JoseOlin/Akoui-Grua/assets/imgs/01_Muestra de operación de la grúa con valeroso modelo.jpg

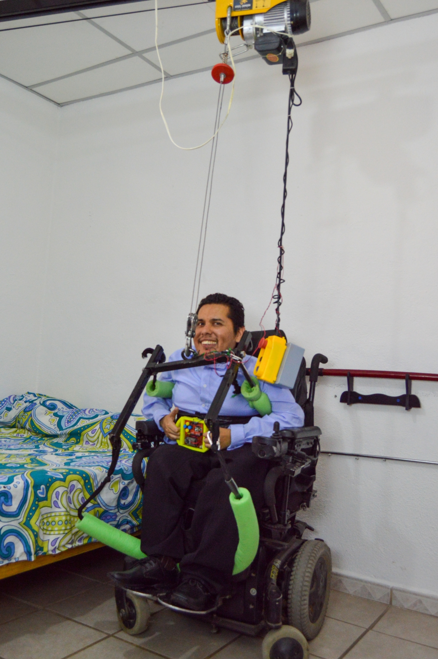
assets/imgs/01_Muestra de operación de la grúa con valeroso modelo.jpg
