JoseOlin/Akoui-Grua/assets/imgs/01_Módulos_Akoui.jpeg

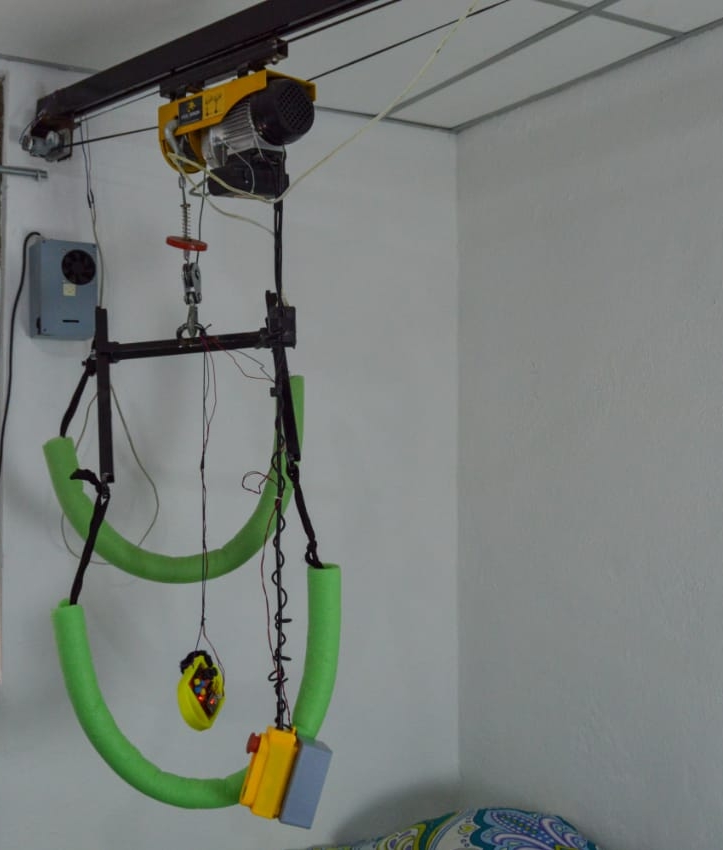
assets/imgs/01_Módulos_Akoui.jpeg
