JoseOlin/Akoui-Grua/assets/imgs/01_Módulos_Akoui_labeled.png

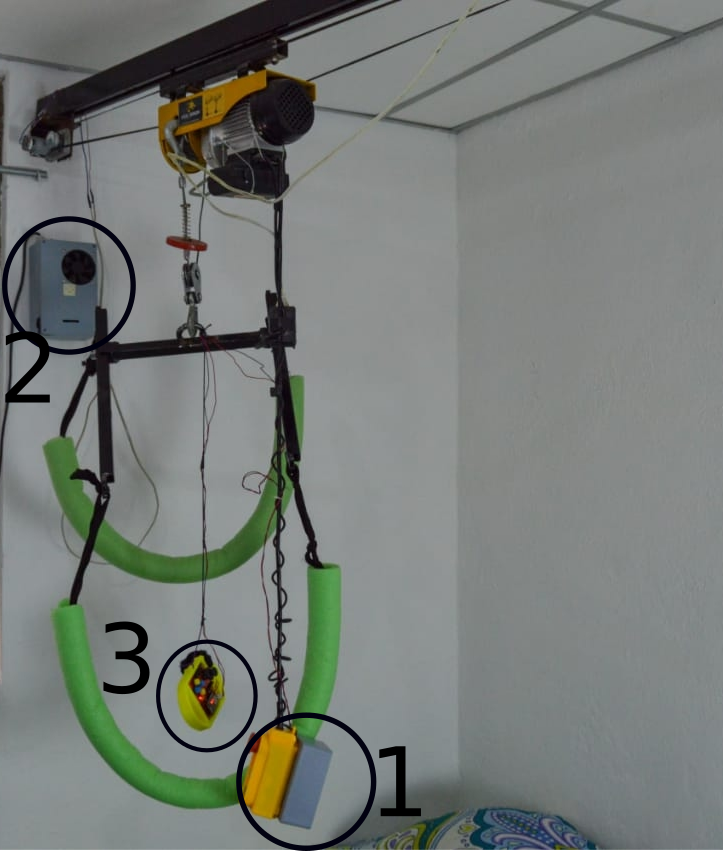
assets/imgs/01_Módulos_Akoui_labeled.png
