JoseOlin/Akoui-Grua/assets/imgs/04_Control de la grúa.png

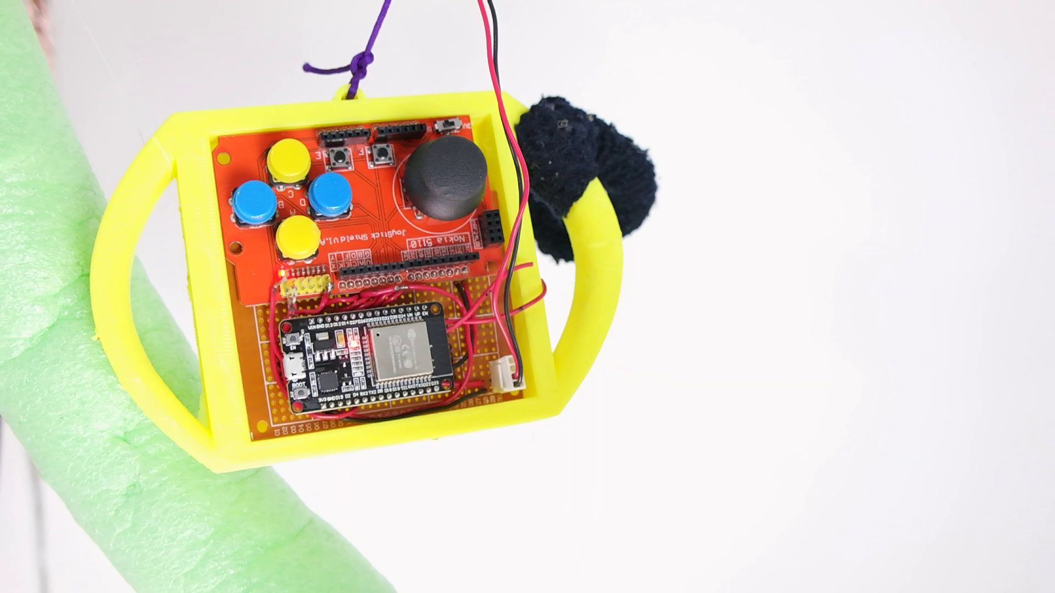
assets/imgs/04_Control de la grúa.png
