JoseOlin/Akoui-Grua/assets/imgs/05_a. Grúa y rieles utilizados para la Akoui.jpeg

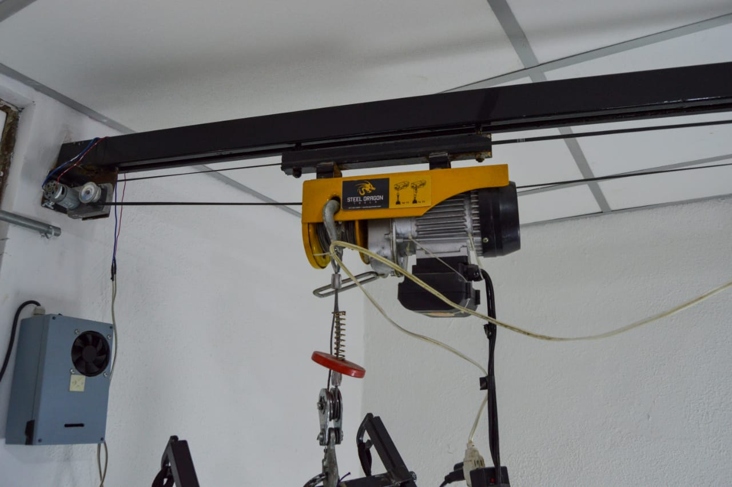
assets/imgs/05_a. Grúa y rieles utilizados para la Akoui.jpeg
