JoseOlin/Akoui-Grua/assets/imgs/diagrama-akoui-pad-control (copia).jpeg

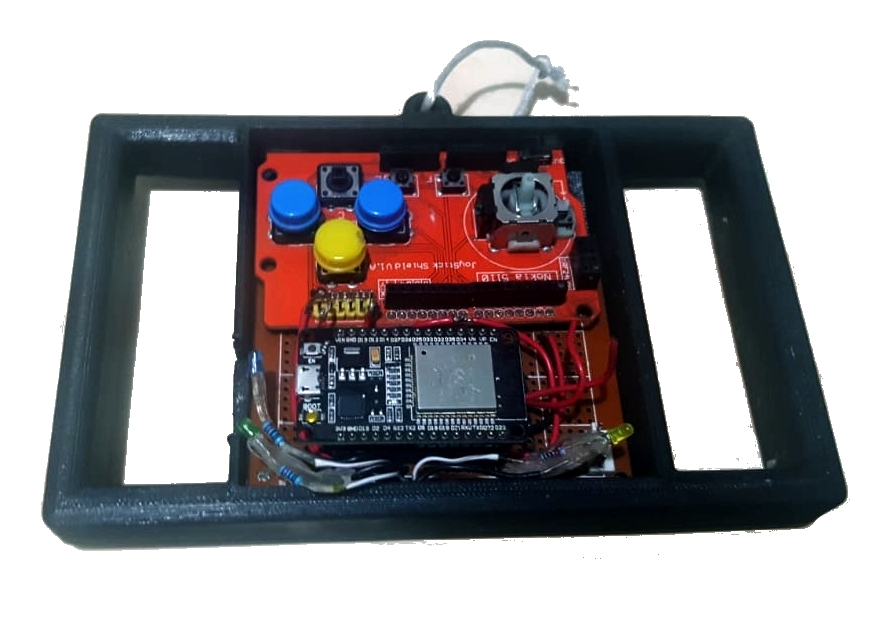
assets/imgs/diagrama-akoui-pad-control (copia).jpeg
