JoseOlin/Akoui-Grua/assets/imgs/IMG_20220910_122807.jpg

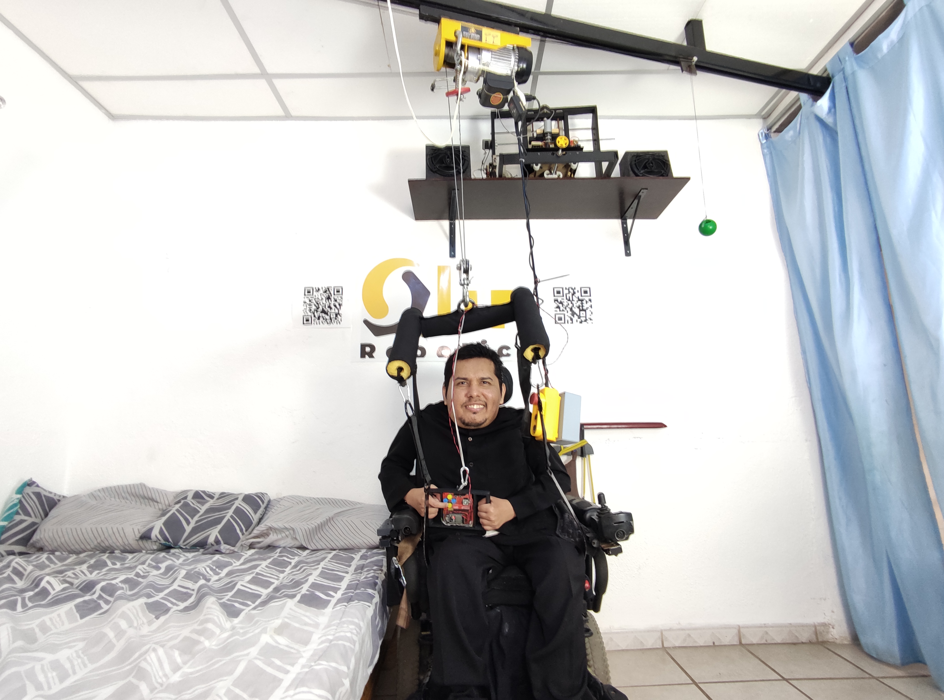
assets/imgs/IMG_20220910_122807.jpg
