JoseOlin/Akoui-Grua/Hardware/Control_Pad/Electronics/Akoui-Pad-Control-Circuit_bb.png

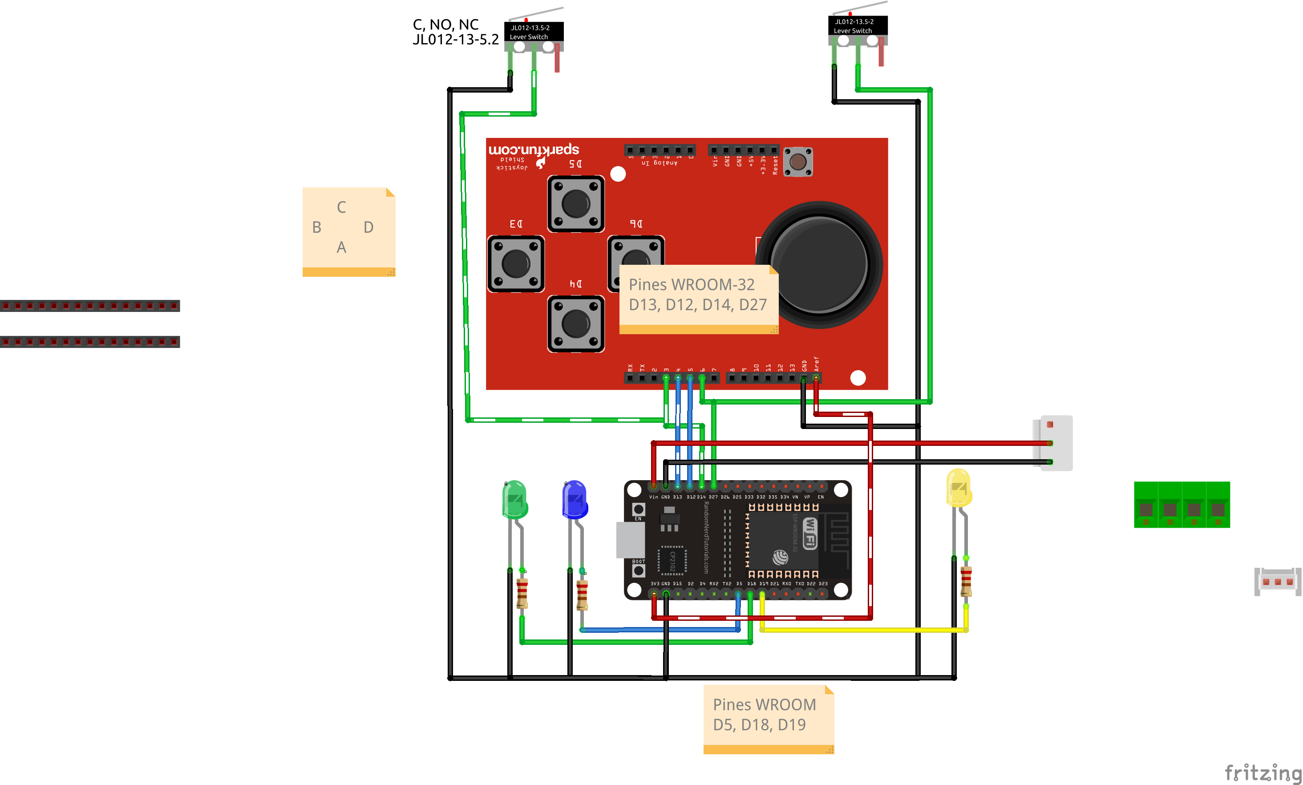
Hardware/Control_Pad/Electronics/Akoui-Pad-Control-Circuit_bb.png
