JoseOlin/Akoui-Grua/Hardware/ModuloControl_Horizontal/Electrónica/PololuMC33926/Pololu_MC33926_pinout.jpg

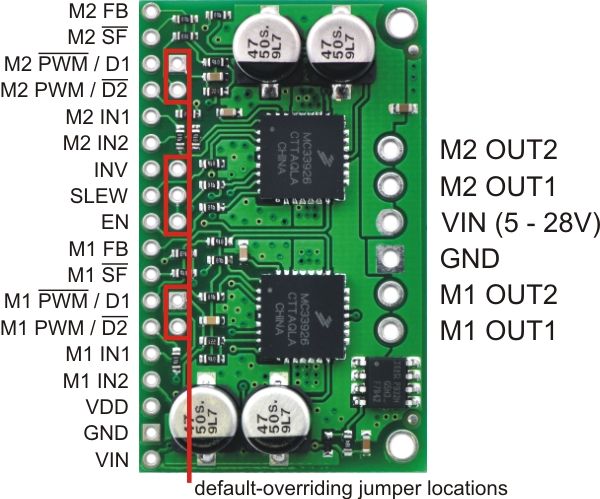
Hardware/ModuloControl_Horizontal/Electrónica/PololuMC33926/Pololu_MC33926_pinout.jpg
