JoseOlin/Akoui-Grua/Hardware/ModuloControl_Horizontal/Electrónica/WeMos_D1_Mini_V2/2dc7d4435c7c950a1209d946ffa383f3e9c8b8a3_2_690x428.jpeg

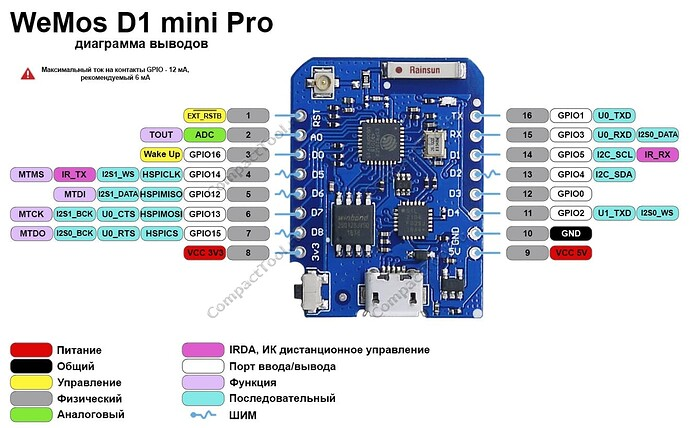
Hardware/ModuloControl_Horizontal/Electrónica/WeMos_D1_Mini_V2/2dc7d4435c7c950a1209d946ffa383f3e9c8b8a3_2_690x428.jpeg
