JoseOlin/Akoui-Grua/Hardware/ModuloControl_Vertical/Electrónica/Circuito/3adffb0e-eeb6-4fb7-9969-0489ad38aaa7.jpeg

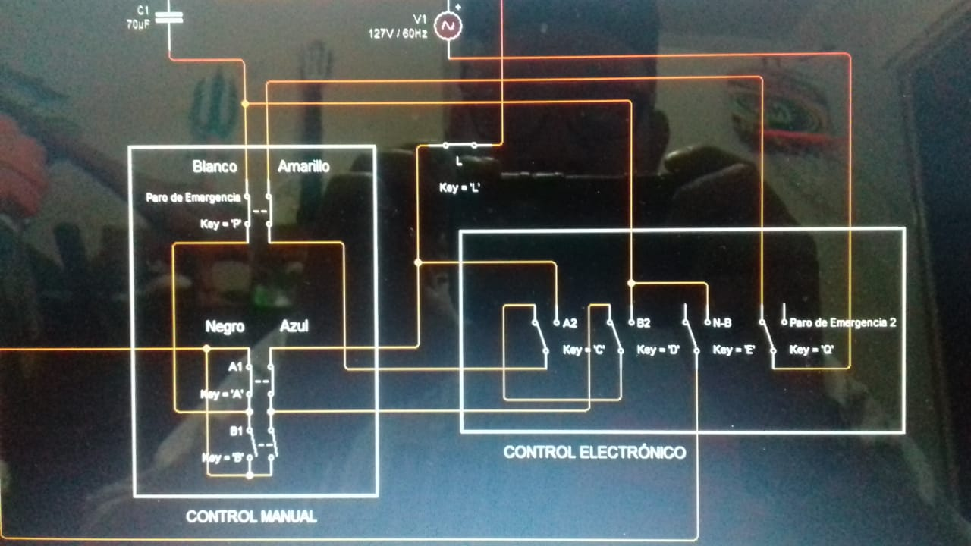
Hardware/ModuloControl_Vertical/Electrónica/Circuito/3adffb0e-eeb6-4fb7-9969-0489ad38aaa7.jpeg
