JoseOlin/Akoui-Grua/Hardware/Riel y Polipasto/36561751_1978189882211582_5358359271018856448_n.jpg

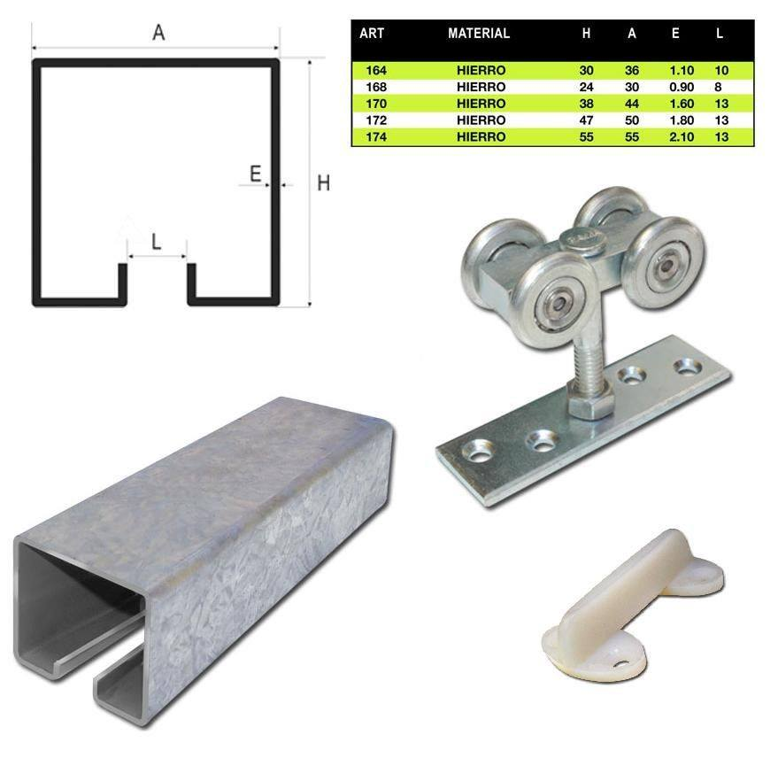
Hardware/Riel y Polipasto/36561751_1978189882211582_5358359271018856448_n.jpg
