JoseOlin/Akoui-Grua/Software/Control_Desktop_QtCreator/ControlGrua_Qt_TCP/imgs/down.jpeg

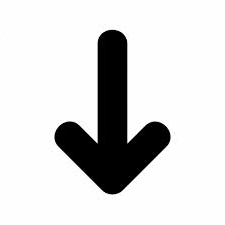
Software/Control_Desktop_QtCreator/ControlGrua_Qt_TCP/imgs/down.jpeg
