JoseOlin/Akoui-Grua/Software/Control_Desktop_QtCreator/ControlGrua_Qt_TCP/imgs/emergency_pressed.jpg

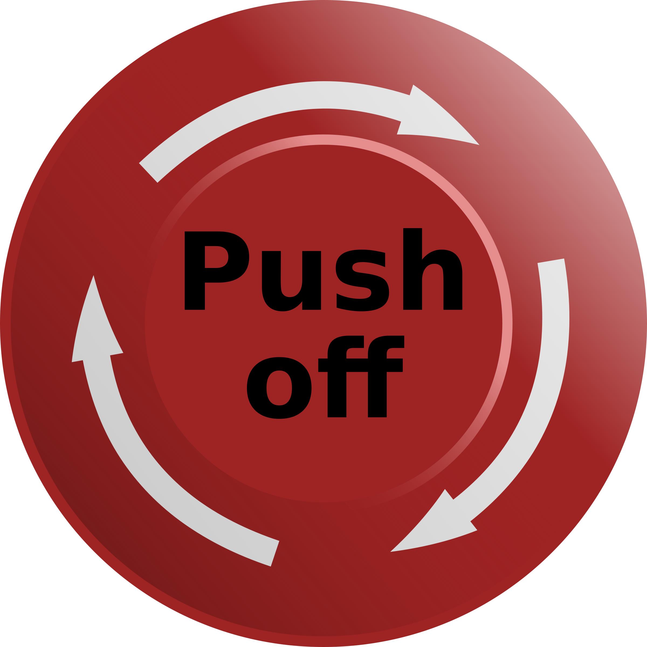
Software/Control_Desktop_QtCreator/ControlGrua_Qt_TCP/imgs/emergency_pressed.jpg
