JoseOlin/Akoui-Grua/Software/Control_Desktop_QtCreator/ControlGrua_Qt_TCP/imgs/emergency_released.png

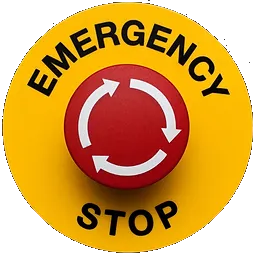
Software/Control_Desktop_QtCreator/ControlGrua_Qt_TCP/imgs/emergency_released.png
