JoseOlin/Akoui-Grua/Hardware/ModuloControl_Vertical/Electrónica/Circuito/Diagrama_ControlManual_Relevadores.jpeg

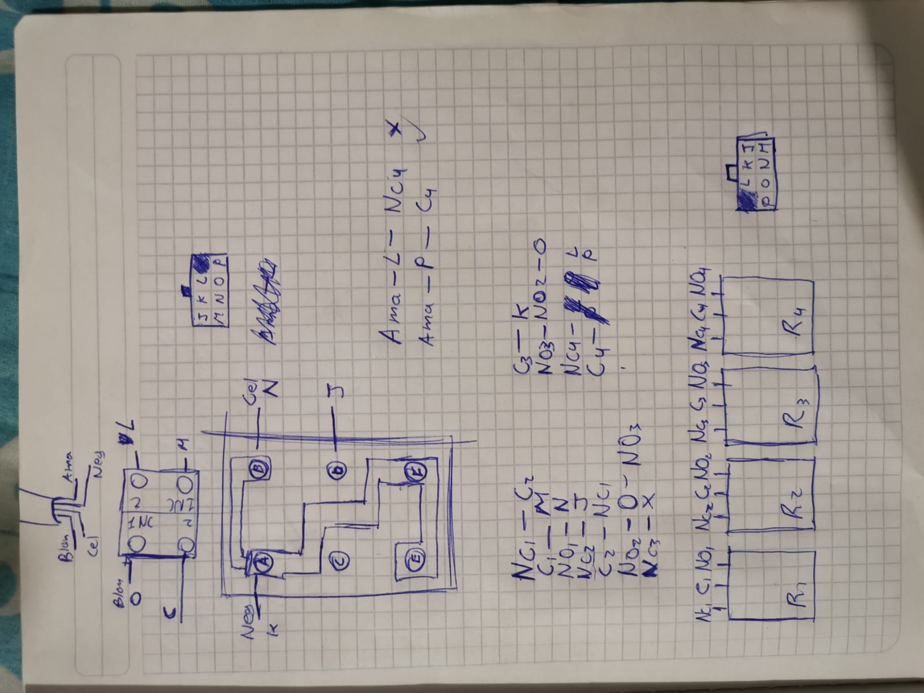
Hardware/ModuloControl_Vertical/Electrónica/Circuito/Diagrama_ControlManual_Relevadores.jpeg
