JoseOlin/Akoui-Grua/Hardware/ModuloControl_Vertical/Electrónica/Circuito/MandoManual2.jpeg

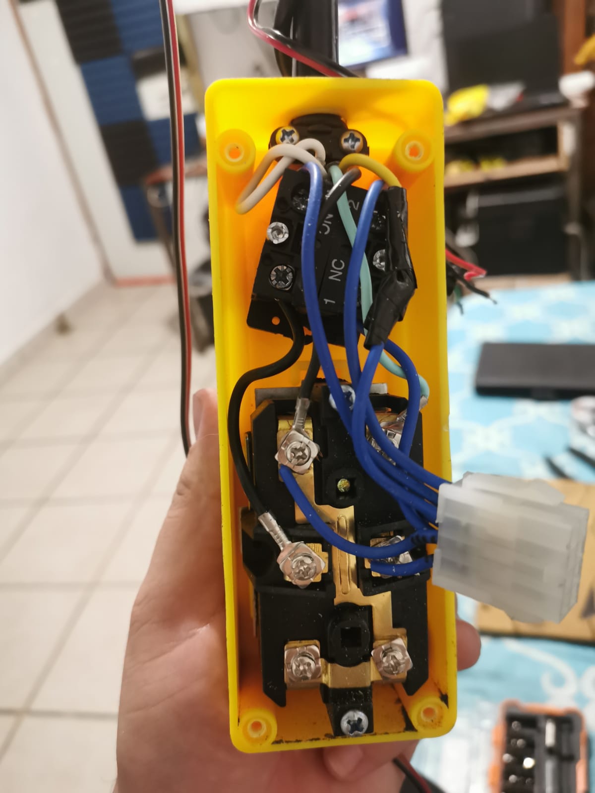
Hardware/ModuloControl_Vertical/Electrónica/Circuito/MandoManual2.jpeg
