JoseOlin/Akoui-Grua/Hardware/ModuloControl_Vertical/Electrónica/Circuito/MandoManual.jpeg

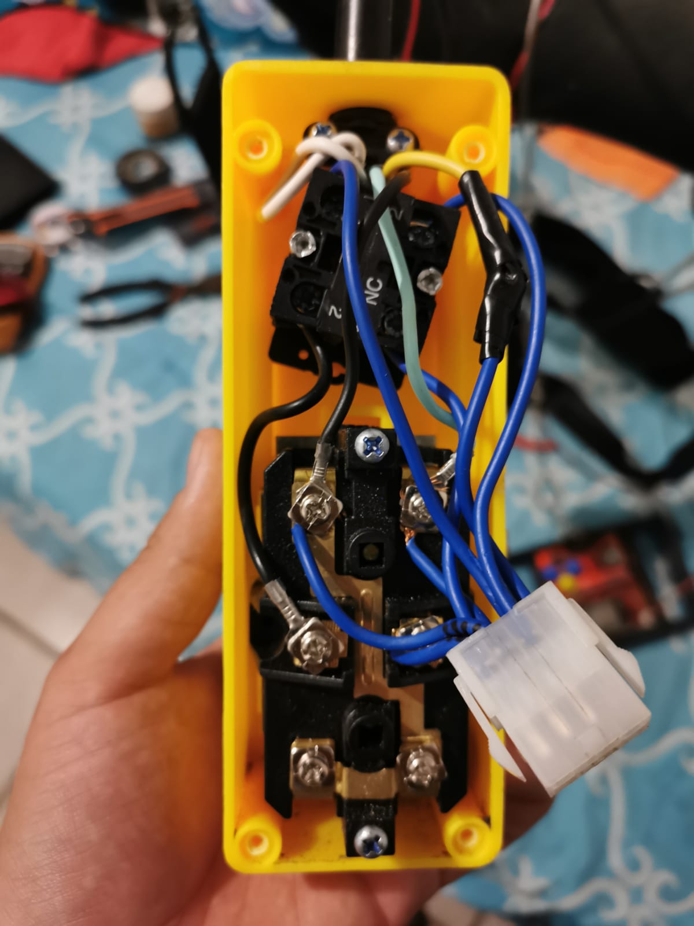
Hardware/ModuloControl_Vertical/Electrónica/Circuito/MandoManual.jpeg
