JoseOlin/Akoui-Grua/Manuals/Manual_Construcción/ControlPad_Construccion/akoui-pio-monitor-con-conexion.gif

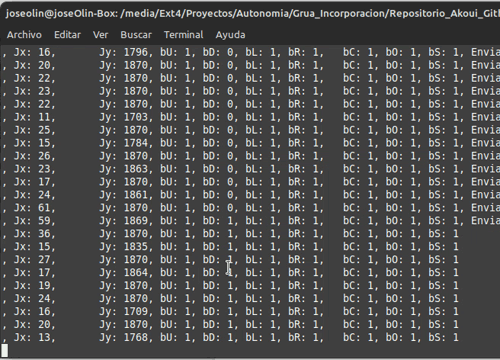
Manuals/Manual_Construcción/ControlPad_Construccion/akoui-pio-monitor-con-conexion.gif
