JoseOlin/Akoui-Grua/Manuals/Manual_Construcción/Instalacion_Riel/imgs/GruaInstalada-2.jpeg

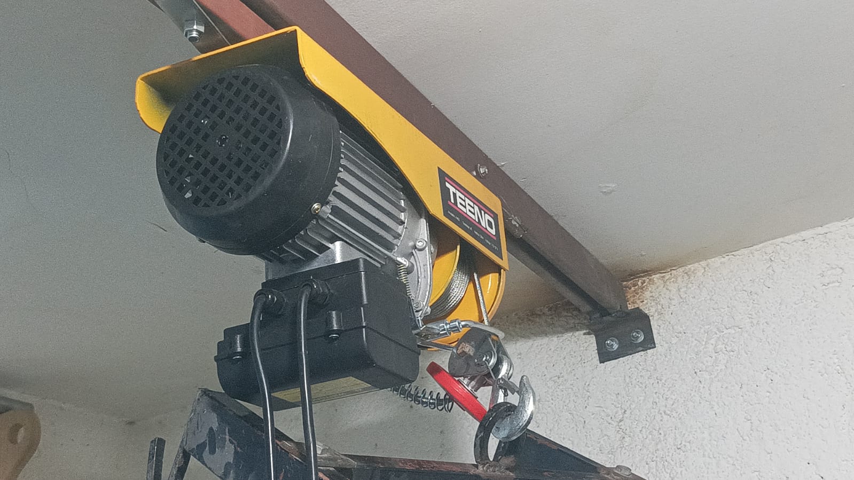
Manuals/Manual_Construcción/Instalacion_Riel/imgs/GruaInstalada-2.jpeg
