JoseOlin/Akoui-Grua/Manuals/Manual_Construcción/Instalacion_Riel/imgs/Instalacion-riel-2.JPG

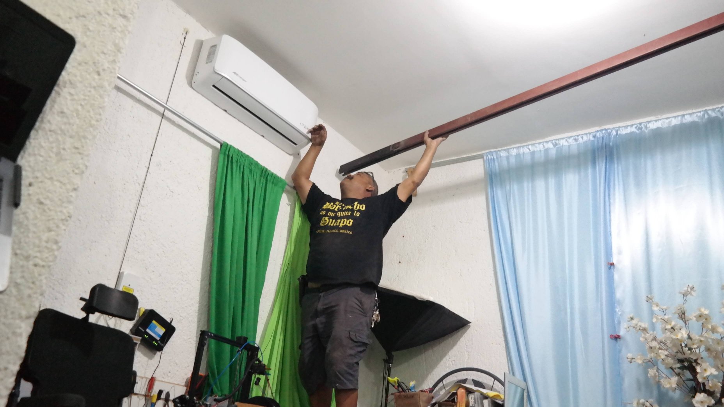
Manuals/Manual_Construcción/Instalacion_Riel/imgs/Instalacion-riel-2.JPG
