JoseOlin/Akoui-Grua/Manuals/Manual_Construcción/Instalacion_Riel/imgs/Instalacion-riel-5.JPG

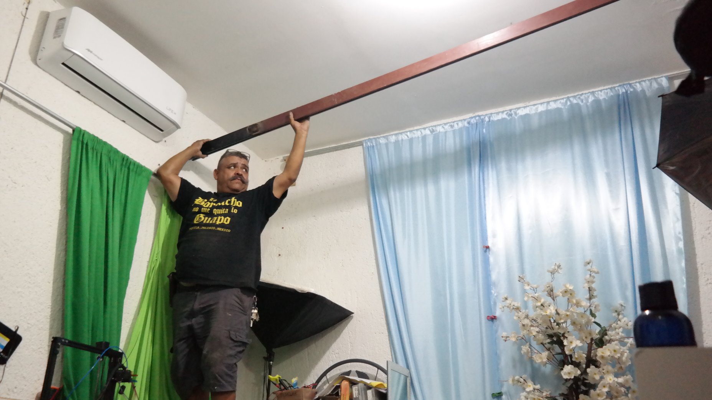
Manuals/Manual_Construcción/Instalacion_Riel/imgs/Instalacion-riel-5.JPG
