JoseOlin/Akoui-Grua/Manuals/Manual_Construcción/Instalacion_Riel/imgs/Instalacion-riel-6.jpeg

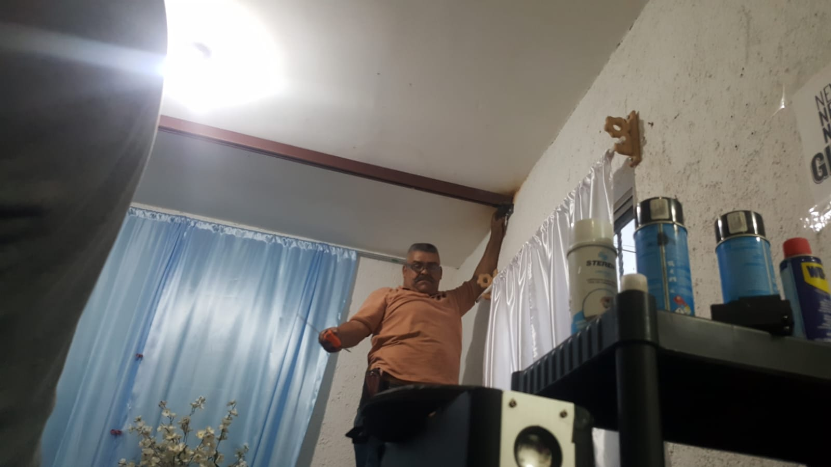
Manuals/Manual_Construcción/Instalacion_Riel/imgs/Instalacion-riel-6.jpeg
