JoseOlin/Akoui-Grua/Manuals/Manual_Construcción/Instalacion_Riel/imgs/Instalacion-riel-7.jpeg

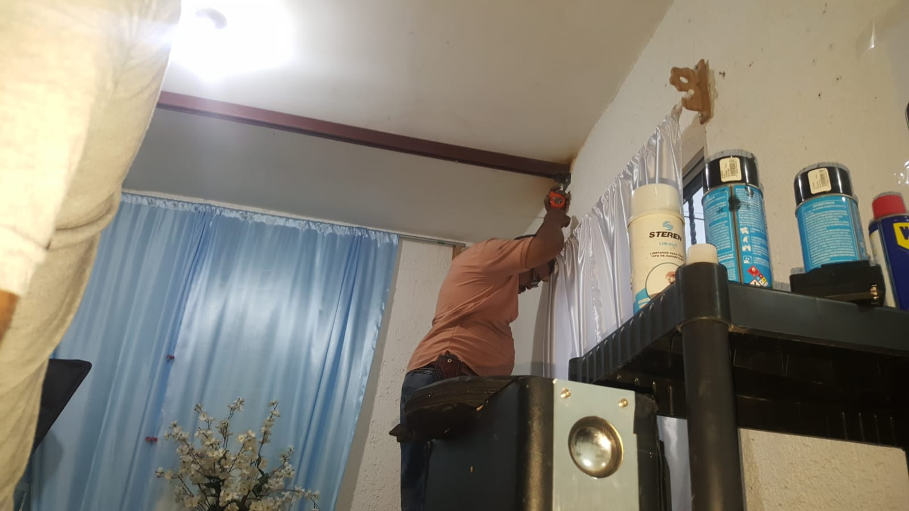
Manuals/Manual_Construcción/Instalacion_Riel/imgs/Instalacion-riel-7.jpeg
