JoseOlin/Akoui-Grua/Manuals/Manual_Construcción/Instalacion_Riel/imgs/Soporte-Angular-Instalado_4.jpeg

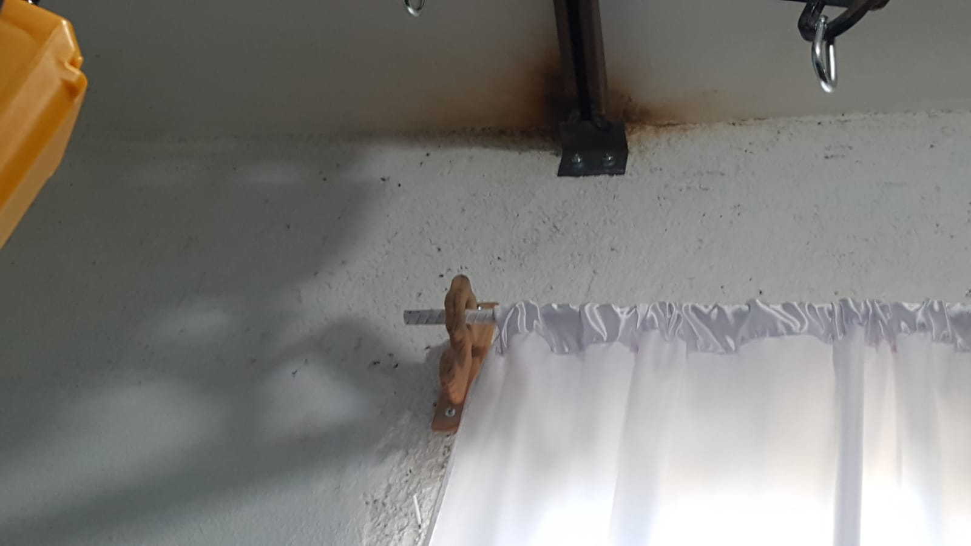
Manuals/Manual_Construcción/Instalacion_Riel/imgs/Soporte-Angular-Instalado_4.jpeg
