JoseOlin/Akoui-Grua/Manuals/Manual_Construcción/Instalacion_Riel/imgs/Soporte-Angular-Instalado_5.jpeg

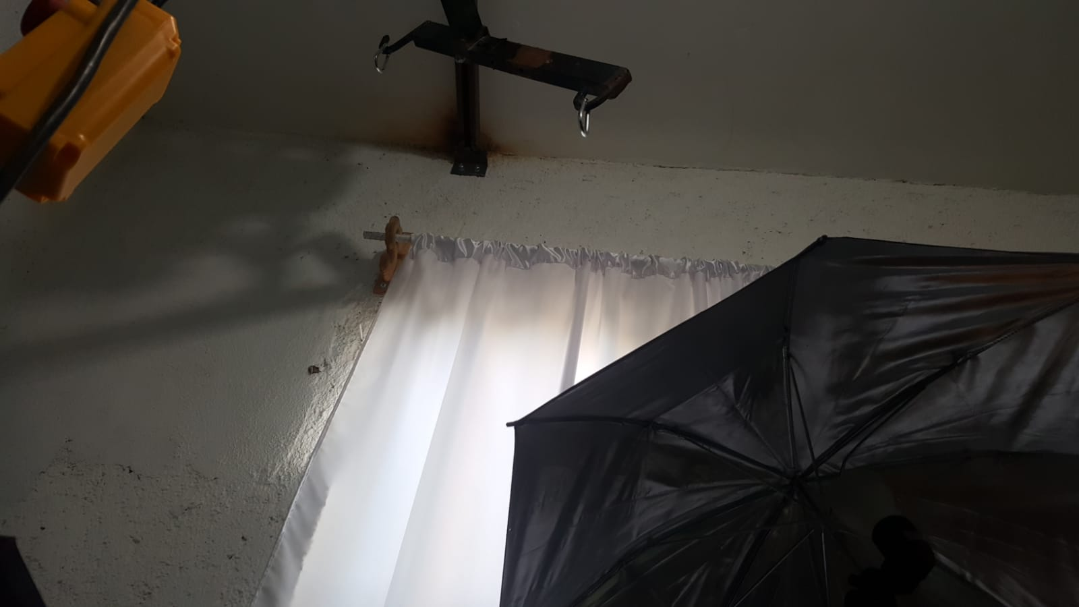
Manuals/Manual_Construcción/Instalacion_Riel/imgs/Soporte-Angular-Instalado_5.jpeg
