JoseOlin/Akoui-Grua/Manuals/Manual_Construcción/Instalacion_Riel/imgs/Soportes_Angulares_8.jpeg

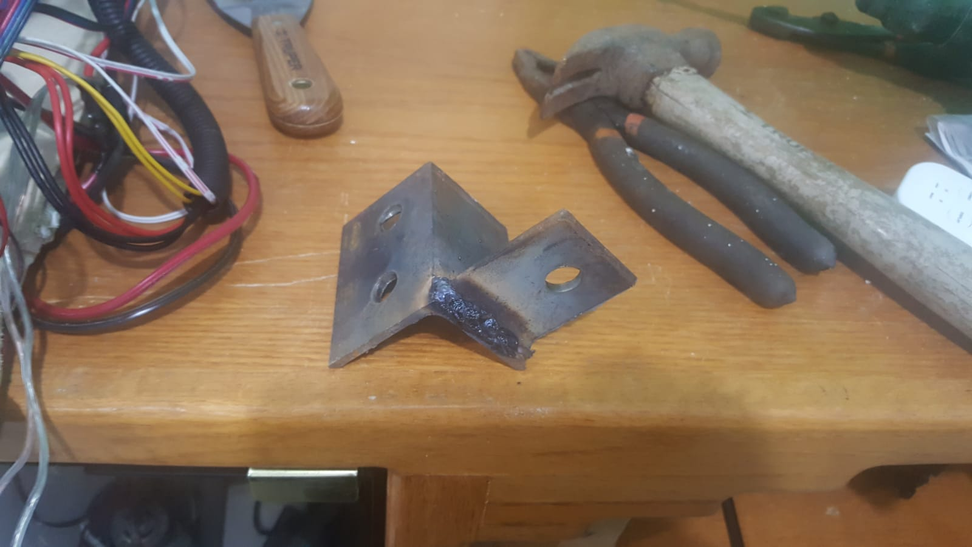
Manuals/Manual_Construcción/Instalacion_Riel/imgs/Soportes_Angulares_8.jpeg
