JoseOlin/Akoui-Grua/Manuals/Manual_Construcción/Instalacion_Riel/imgs/Soportes_Angulares_9.jpeg

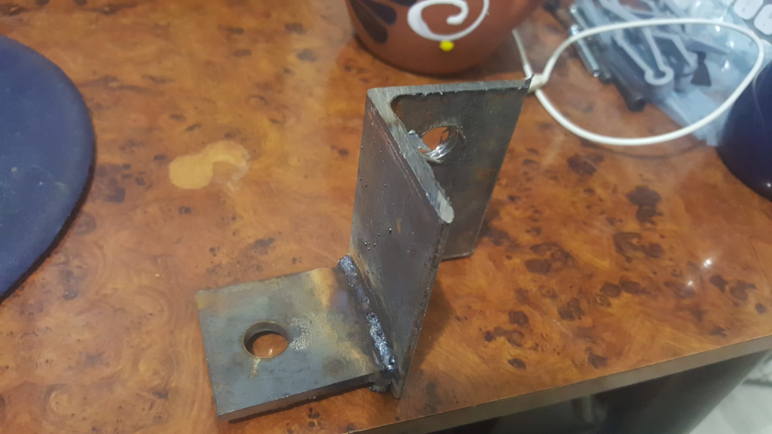
Manuals/Manual_Construcción/Instalacion_Riel/imgs/Soportes_Angulares_9.jpeg
