JoseOlin/Akoui-Grua/Manuals/Manual_Construcción/Instalacion_Riel/imgs/taquetes_6.jpeg

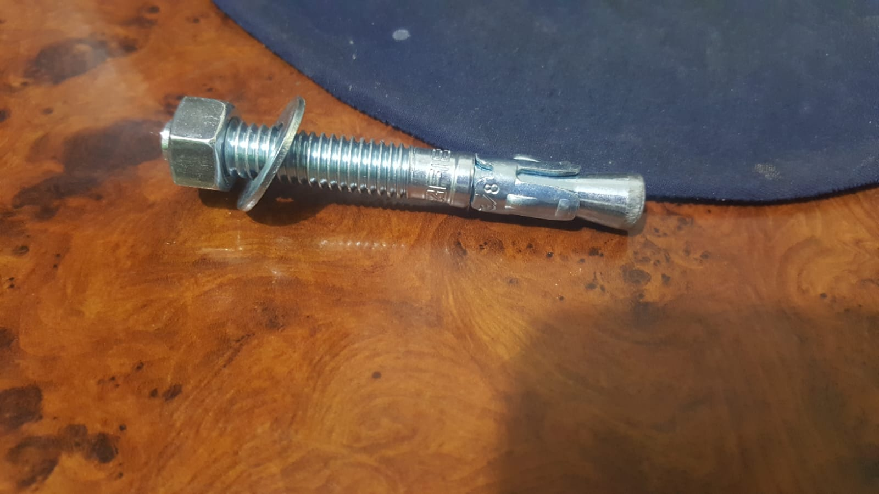
Manuals/Manual_Construcción/Instalacion_Riel/imgs/taquetes_6.jpeg
