JoseOlin/Akoui-Grua/Manuals/Manual_Construcción/Instalacion_Riel/imgs/Tornillo_3-8_3.jpeg

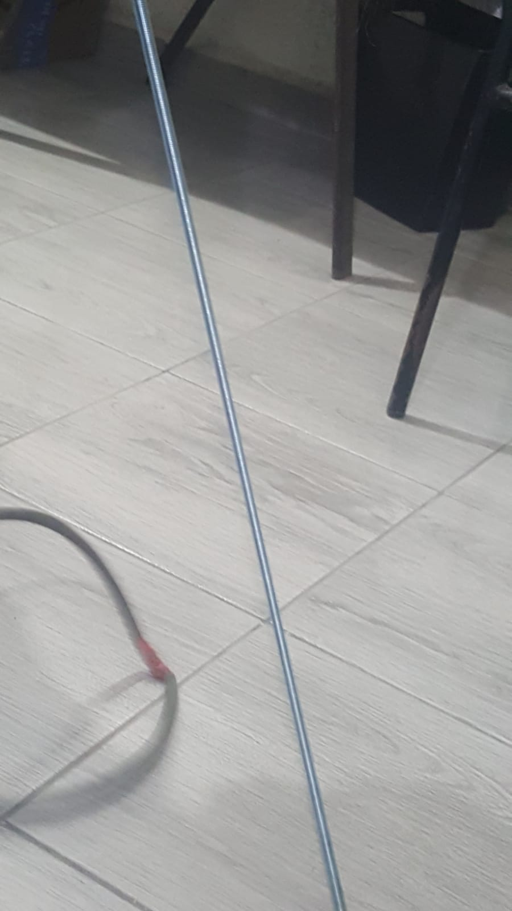
Manuals/Manual_Construcción/Instalacion_Riel/imgs/Tornillo_3-8_3.jpeg
