JoseOlin/Akoui-Grua/Manuals/Manual_Construcción/Instalacion_Riel/imgs/Tornillo_3-8_Recortado_1.JPG

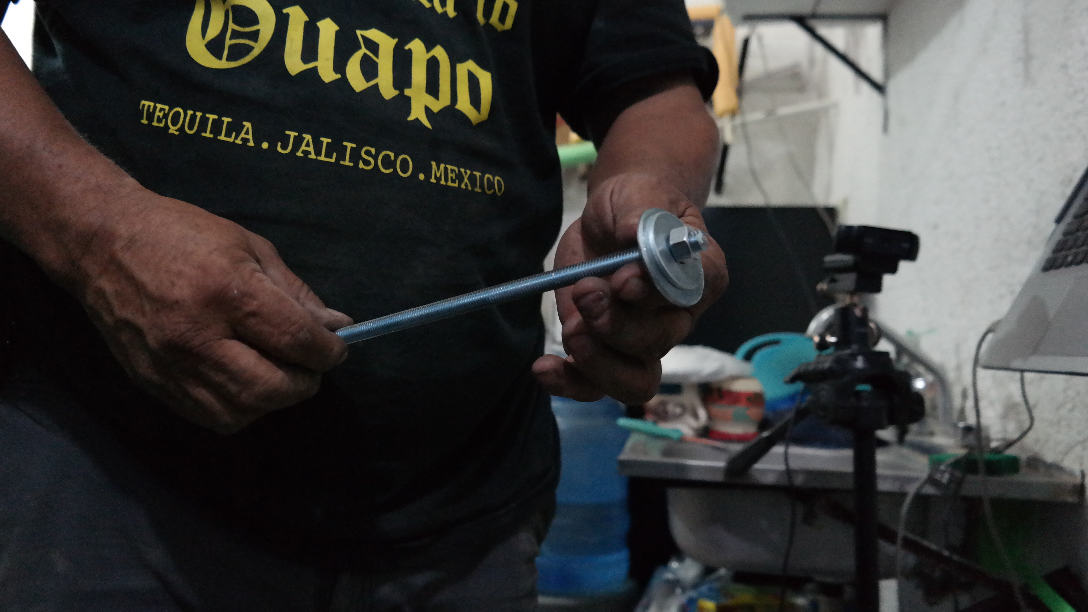
Manuals/Manual_Construcción/Instalacion_Riel/imgs/Tornillo_3-8_Recortado_1.JPG
