JoseOlin/Akoui-Grua/Manuals/Manual_Mantenimiento/imgs/7e57e645-24a5-4c56-a8ba-4ad31c3c1ef6.jpeg

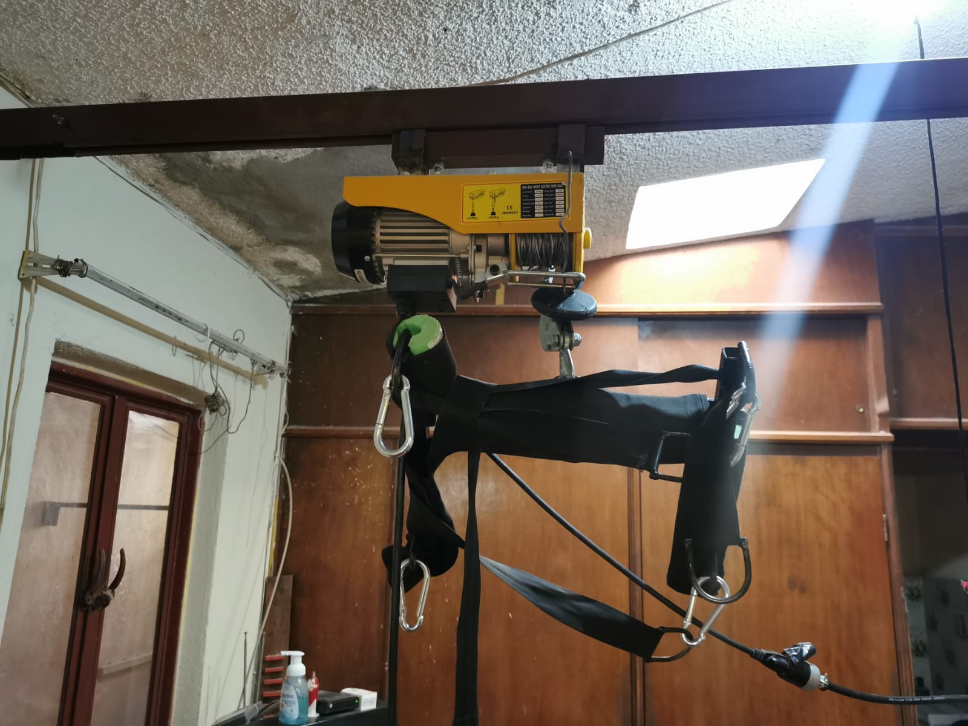
Manuals/Manual_Mantenimiento/imgs/7e57e645-24a5-4c56-a8ba-4ad31c3c1ef6.jpeg
