JoseOlin/Akoui-Grua/Manuals/Manual_Mantenimiento/imgs/87ca44ee-71d5-4784-a0d1-1c792c2dc31c.jpeg

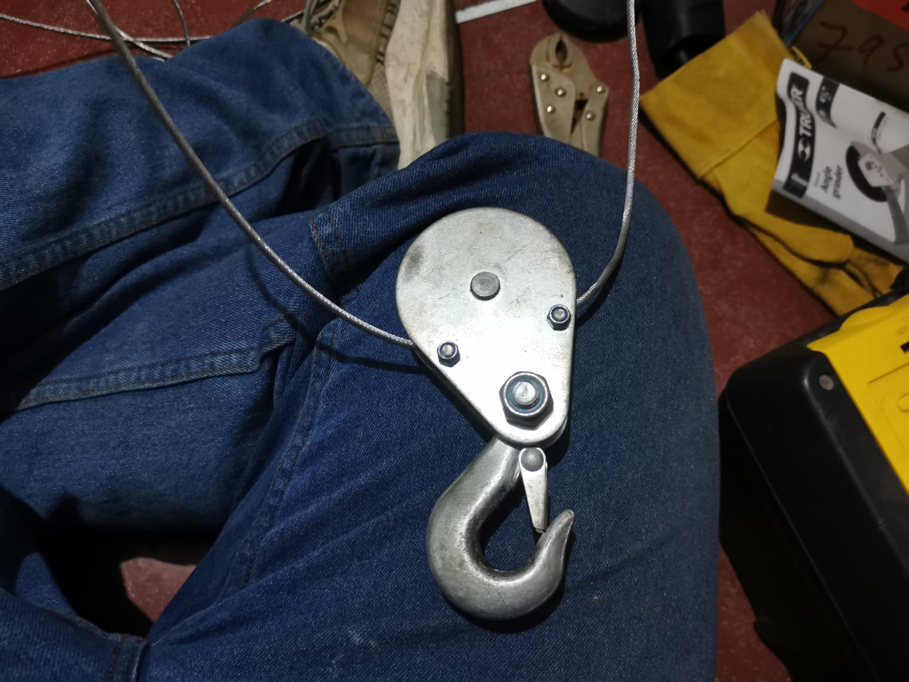
Manuals/Manual_Mantenimiento/imgs/87ca44ee-71d5-4784-a0d1-1c792c2dc31c.jpeg
