JoseOlin/Akoui-Grua/Manuals/Manual_Mantenimiento/imgs/94c086cd-e113-414c-a847-a976a1d2ec9f.jpeg

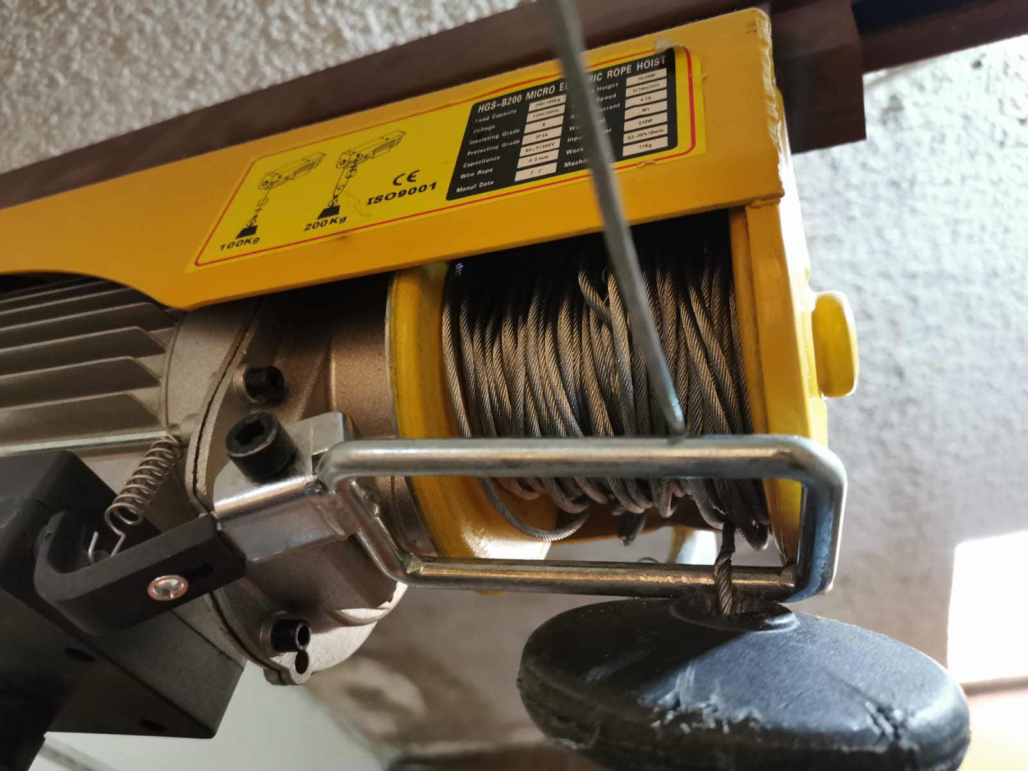
Manuals/Manual_Mantenimiento/imgs/94c086cd-e113-414c-a847-a976a1d2ec9f.jpeg
