JoseOlin/Akoui-Grua/Manuals/Manual_Mantenimiento/imgs/622aca14-799e-4082-832f-13193dbb039a.jpeg

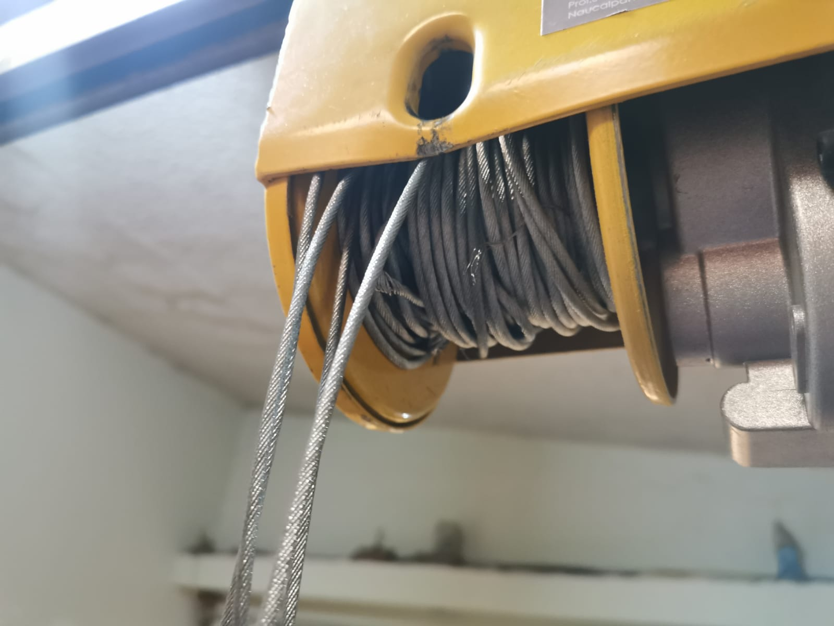
Manuals/Manual_Mantenimiento/imgs/622aca14-799e-4082-832f-13193dbb039a.jpeg
