JoseOlin/Akoui-Grua/Manuals/Manual_Mantenimiento/imgs/7469d51a-8d23-431f-8460-3a72f369e754.jpeg

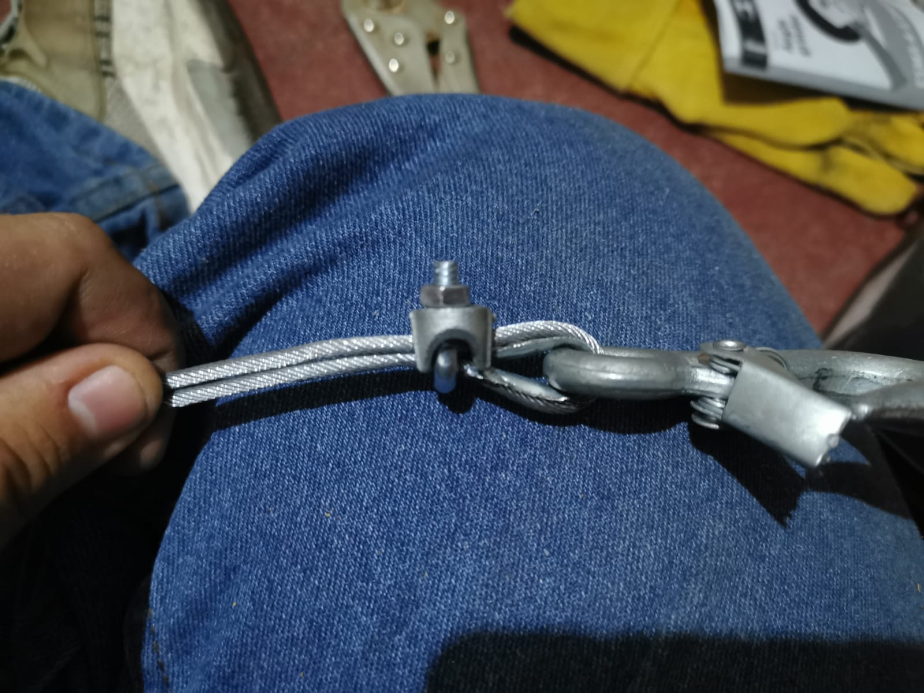
Manuals/Manual_Mantenimiento/imgs/7469d51a-8d23-431f-8460-3a72f369e754.jpeg
