JoseOlin/Akoui-Grua/Manuals/Manual_Mantenimiento/imgs/a559afcb-1f23-4249-970f-1458fe0535cf.jpeg

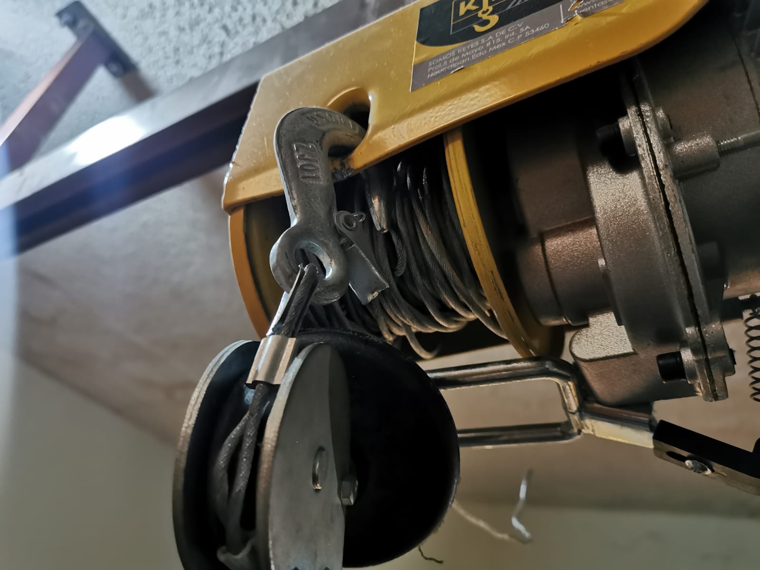
Manuals/Manual_Mantenimiento/imgs/a559afcb-1f23-4249-970f-1458fe0535cf.jpeg
