JoseOlin/Akoui-Grua/Manuals/Manual_Mantenimiento/imgs/e9713eeb-e923-46fa-aeeb-5184e3b0482e.jpeg

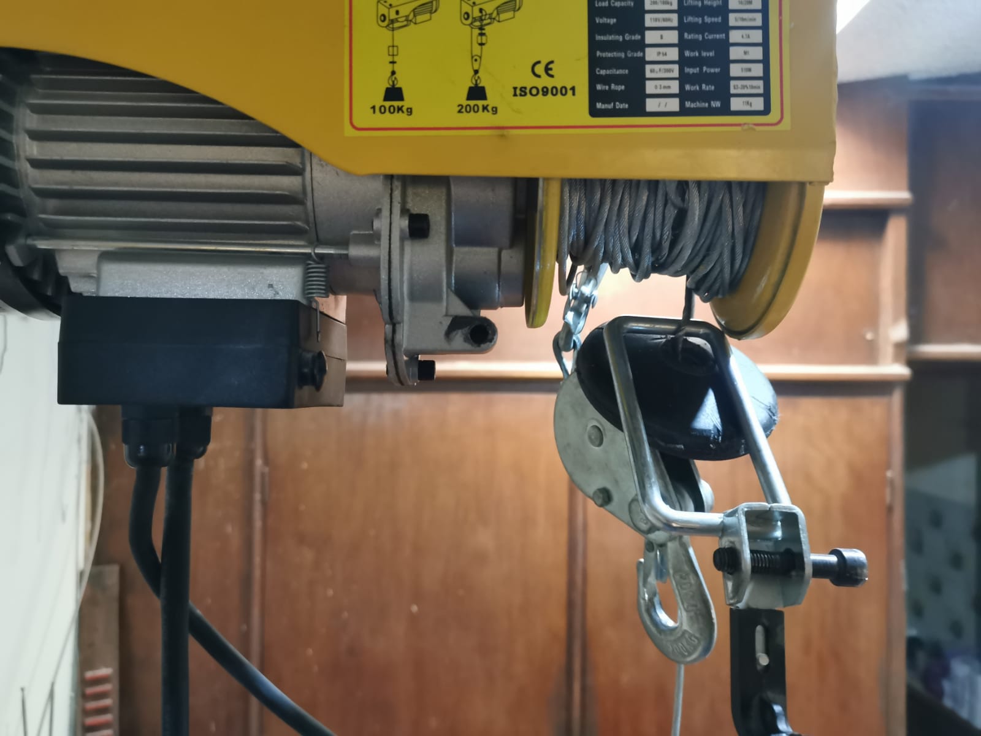
Manuals/Manual_Mantenimiento/imgs/e9713eeb-e923-46fa-aeeb-5184e3b0482e.jpeg
