JoseOlin/Akoui-Grua/Manuals/Manual_Mantenimiento/imgs/f397b851-9fc2-478f-b968-d5da6280be08.jpeg

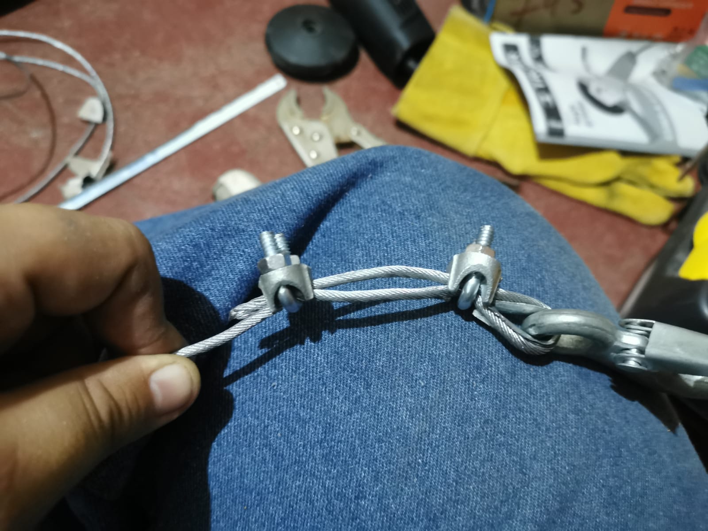
Manuals/Manual_Mantenimiento/imgs/f397b851-9fc2-478f-b968-d5da6280be08.jpeg
